SenyoraDeSombras/physical-dashboard/dashboard.kicad_sch

## KiCad design dashboard.kicad_sch (2026-05-14)

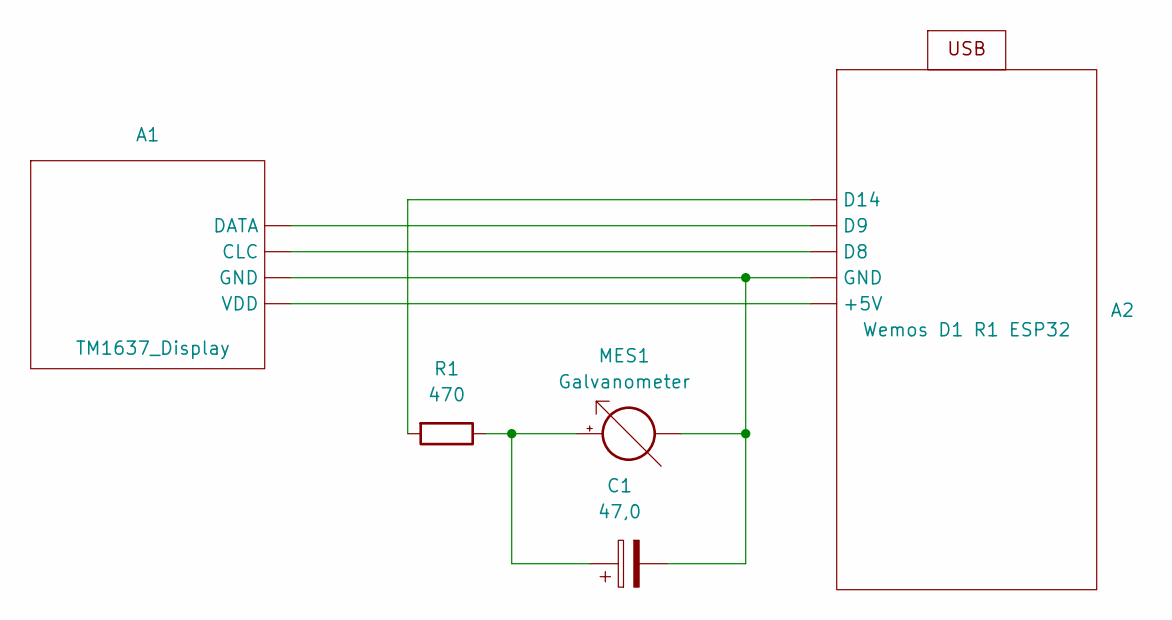
[picture p3: schematic dashboard.kicad_sch]

Parts:
A1: TM1637_Display
A2: Wemos D1 R1 ESP32
C1: 47,0
MES1: Galvanometer
R1: 470

Connections:
unnamed: A1., A2., C1.2, MES1.1 (-)
unnamed: A2., R1.2
unnamed: C1.1, MES1.2 (+), R1.1
